Envious-Data/EnvOpenPico/_photos/DSC_2514.JPG

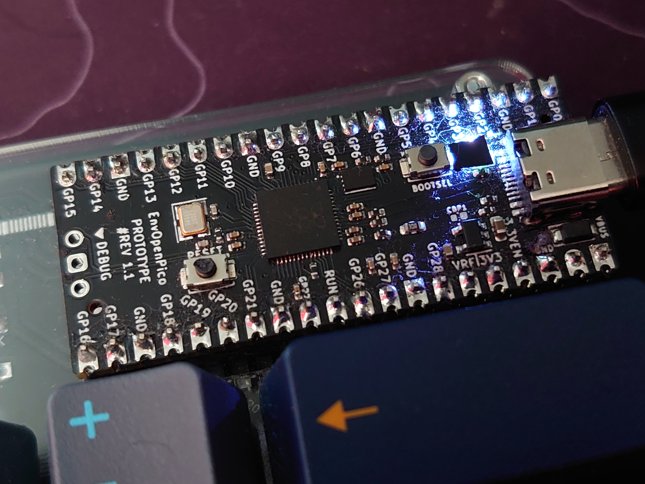
_photos/DSC_2514.JPG
